nickthelegend/ripar-wallet/docs/FIRMWARE.md

# Ripar Wallet: firmware guide

The firmware turns a Waveshare ESP32-S3-LCD-2 into an air-gapped signer. Its radio is off. Requests arrive as QR codes through the camera, and every answer leaves as one QR code on the screen. Nothing is signed until the user has seen every line of the review, held a thumb on the pulse sensor until a live pulse is measured, and then pressed SIGN.

- **Protocol:** byte-exact contract in [`PROTOCOL.md`](PROTOCOL.md).
- **Bluetooth fallback:** the builds `env:ripar` and `env:ripar-ble` can also carry the same QR text over Bluetooth LE when the camera cannot read the codes. The radio stays dead until the user turns it on in the device menu (review + pulse + SIGN), and every screen shows **RADIO ON** while it is alive. `env:ripar-airgap` is the same firmware without any radio code. Contract: [`BLE_LINK.md`](BLE_LINK.md); on the device: [BLE LINK](#ble-link-bluetooth-fallback).
- **Wi-Fi test link (TEMPORARY TEST FEATURE):** the default build `env:ripar` also contains a Wi-Fi courier for testing (`RIPAR_WIFI=1`): the network is sent by the paired phone over Bluetooth and confirmed on the device, Wi-Fi runs only after **WI-FI ON** in the menu, and every screen shows **WIFI ON** while it is alive. **For the air-gapped pitch firmware flash `env:ripar-airgap`** (or `env:ripar-ble` for Bluetooth without Wi-Fi). Contract: [`WIFI_LINK.md`](WIFI_LINK.md); on the device: [Wi-Fi test link](#wi-fi-test-link-temporary).
- **Wiring:** full pin list in [`WIRING.md`](WIRING.md).
- **Source:** `firmware/` (PlatformIO, Arduino-ESP32 2.0.17 / ESP-IDF 4.4).

> **Status (2026-09-27, firmware v1.2).** The full firmware builds and links. The host tests cover the portable code, including the screen state machine, the signing gate, the SIGN step (byte-equal to the Python reference) and the vault derivation, and they pass. Firmware v1.2 compiles in the Ripar contract addresses, derives the vault from K1, stores context layout v3 and enforces PANIC FIRST ([PROTOCOL.md §7](PROTOCOL.md#7-changes-in-firmware-v12)). The findings of the second security and conformance review (panic epoch, re-pairing, key presses across screens, device-time ratchet, sentinel, revoke display) are fixed in code and tests; what stays open is listed under [Known limitations](#known-limitations). The QR frames drawn by `companion_lite.html` decode with the firmware's own quirc + UR decoder + parser on the PC. **Nothing in this guide has been checked on a real board yet**: the display rotation, the camera orientation, the pulse-sensor tuning and the key timings are all untested. See [Known limitations](#known-limitations).

## Contents

1. [Hardware and wiring](#1-hardware-and-wiring)
2. [Build and test](#2-build-and-test)
3. [Flash over USB-C](#3-flash-over-usb-c)
4. [First boot](#4-first-boot)
5. [Screens and keys](#5-screens-and-keys)
6. [Walkthrough](#6-walkthrough)
7. [Security model](#7-security-model)
8. [Known limitations](#known-limitations)
9. [Source map](#9-source-map)

## 1. Hardware and wiring

| Part | Connection | Notes |
|---|---|---|
| Waveshare ESP32-S3-LCD-2 | - | ESP32-S3R8 (8 MB octal PSRAM), 16 MB flash, 2" ST7789 LCD used landscape at 320×240 |
| OV5640 camera | 24-pin FPC on the back | grayscale QVGA, powered down between scans |
| MAX30102 pulse sensor | VIN → 3V3 (P2-1), GND → P2-2, SDA → **GPIO48** (P2-6), SCL → **GPIO47** (P2-5), INT open | shares the I2C bus with the on-board IMU (0x6B). **Move its pull-up jumper to 3.3 V.** |
| Buzzer (active, 3.3 V) | + → **GPIO18** (P1-6), − → GND | use an S8050 + 1 k base resistor for a 5 V buzzer or one drawing more than 20 mA |
| SIGN key | the board's **BOOT key (GPIO0)**, pressed by the printed Sign_Pin | a strapping pin: **never hold it while powering on** |
| Battery | 18650 → TP4056 → latching switch → board BAT connector | the gauge reads GPIO5 through the board's 200 k / 100 k divider |

With the camera attached, the only free signals are GPIO18, GPIO43 and GPIO44, plus the shared I2C bus. `firmware/include/board.h` holds every pin.

## 2. Build and test

Requirements: PlatformIO Core and Python 3 (standard library only). `lib_deps` fetches LovyanGFX once. The quirc QR decoder is vendored in `firmware/lib/quirc`.

```bash
cd firmware
pio run -e ripar            # TEST build (default): QR + Bluetooth LE fallback + Wi-Fi test link -> .pio/build/ripar/firmware.bin
pio run -e ripar-ble        # QR + Bluetooth LE fallback, no Wi-Fi code -> .pio/build/ripar-ble/firmware.bin
pio run -e ripar-airgap     # the air-gapped firmware, no radio code at all -> .pio/build/ripar-airgap/firmware.bin
pio run -e chk_device       # device bring-up check (no signing code), see test/device/check_main.cpp
python test/host/run_host_tests.py          # portable modules, MinGW / any g++ as C++14
python tools/make_request.py selftest       # companion tool: build -> simulate -> verify, tamper tests
python tools/make_request.py check-vectors  # test/host/vectors_protocol.h matches the Python reference
python tools/ref_eip712.py check            # test/host/vectors_eip712_abi.h matches the Python reference
```

- The host suites are `test_ble_link`, `test_cbor_ur`, `test_crypto`, `test_eip712_abi`, `test_fsm`, `test_hashes`, `test_policy`, `test_protocol`, `test_pulse`, `test_respond`, `test_vault` and `test_wifi_link`.
- Three firmware builds (the only differences are `RIPAR_BLE` and `RIPAR_WIFI`):

| Env | `RIPAR_BLE` | `RIPAR_WIFI` | What it is | Last build (2026-09-28), of 327 680 B RAM / 6 553 600 B flash |
|---|---|---|---|---|
| `ripar` (default) | 1 | 1 | **test build**: QR + the Bluetooth LE fallback courier + the Wi-Fi test link (`src/wifi_link.cpp`, `src/wifi_proto.cpp`) | RAM 27.5 % (90 024 B), flash 26.8 % (1 759 157 B) |
| `ripar-ble` | 1 | 0 | QR + the Bluetooth LE fallback courier (`src/ble_link.cpp`, `src/ble_proto.cpp`); no Wi-Fi code linked | RAM 20.3 % (66 568 B), flash 20.5 % (1 345 909 B) |
| `ripar-airgap` | 0 | 0 | **the air-gapped firmware**: no BLE / Wi-Fi source built, no Bluetooth / Wi-Fi code linked ([radio check](#7-security-model)) | RAM 12.1 % (39 572 B), flash 11.3 % (738 921 B) |

- The sizes are static RAM and flash in the default 16 MB partition table. While a radio is on, Bluedroid / the Wi-Fi driver and lwIP also allocate heap (not measured on hardware). The ERC1967Proxy creation code of the vault derivation (1008 bytes) lives in flash.
- `pio run -t compiledb` without the same `PLATFORMIO_BUILD_FLAGS` as the last build changes the configuration hash, and PlatformIO then empties `.pio/build/<env>`: build again afterwards.
- A low-disk PC can add `PLATFORMIO_BUILD_FLAGS=-pipe` so that GCC keeps its temporary files in memory. Run one `pio` build at a time.
- Optional build flags (add them to `build_flags`):

| Flag | Default | Meaning |
|---|---|---|
| `RIPAR_BLE` | 1 in `ripar` and `ripar-ble`, 0 in `ripar-airgap` | The Bluetooth LE fallback courier ([BLE_LINK.md](BLE_LINK.md)). Use the envs rather than setting it by hand: `ripar-airgap` also leaves the BLE sources out. |
| `RIPAR_WIFI` | 1 in `ripar`, 0 in `ripar-ble` and `ripar-airgap` | The Wi-Fi test link ([WIFI_LINK.md](WIFI_LINK.md)), a TEMPORARY TEST FEATURE. Needs `RIPAR_BLE=1`. Use the envs: `ripar-ble` / `ripar-airgap` also leave the Wi-Fi sources and libraries out. |
| `RIPAR_LCD_ROTATION` | 1 | Use 3 if the screen is upside down. |
| `RIPAR_CAM_VFLIP` / `RIPAR_CAM_HMIRROR` | 1 / 0 | Viewfinder orientation. QR decoding works either way. |
| `RIPAR_CAM_AE_LEVEL` | -2 | Camera exposure. Go darker (down to -4) if phone screens wash out. |
| `RIPAR_PULSE_STRICT` | 0 on the device, 1 in the emulator | 1 adds the strict anti-spoof liveness tests (beat-timing variability, pulse shape, IR/red cross-timing) to the standard pulse gate. **Off on the device**: on the first hardware test they rejected a real resting thumb (82 bpm, very low beat-to-beat variability). See [Pulse gate: standard and strict](#pulse-gate-standard-and-strict). |
| `RIPAR_CHECK_START_PULSE` / `RIPAR_CHECK_RAW` | unset | `chk_device` only: start on the pulse screen / stream raw MAX30102 samples (`raw,<n>,<ir>,<red>` at 100 Hz) for `tools/pulse_replay`. |
| `RIPAR_LED_CHALLENGE` | 0 | 1 also requires the MAX30102 LED-drive liveness challenge before SIGN is armed. Not tested on hardware. |
| `RIPAR_TIME_FLOOR` | 2026-09-26 00:00 UTC | The earliest "now" the device assumes (see [co-sign expiry](#co-sign)). |

## 3. Flash over USB-C

Use the board's own USB-C port, not the charge-only TP4056 port. Never plug both at once.

```bash
cd firmware
pio run -e ripar -t upload          # builds if needed, then flashes over the native USB (USB-Serial/JTAG)
pio device monitor -b 115200        # optional: status lines (self-test, K1 address, "output <type>")
```

**If the upload cannot connect** (a crashed app, or a USB port that no longer enumerates), use ROM download mode:

1. Hold **BOOT**.
2. Press and release **RST**.
3. Release **BOOT**. The chip now waits in ROM download mode, and the screen stays dark.
4. Run `pio run -e ripar -t upload` again.
5. Press **RST** to start the new firmware.

`ripar` is the **test build** (with the temporary Wi-Fi test link). For a demo, a pitch or funds flash `pio run -e ripar-airgap -t upload` (no radio code) or `-e ripar-ble` (Bluetooth fallback, no Wi-Fi code).

A normal upload does not touch the NVS partition, so the seed and the pairing survive re-flashing (and so does a stored Wi-Fi network: FORGET WI-FI before flashing another build if its password matters).

> **`pio run -t erase` erases the whole flash, including the seed.** The device then creates new keys, which means a new K1 address and a new vault owner. There is no seed backup yet (see [Known limitations](#known-limitations)). Only erase a unit that holds no funds.

## 4. First boot

| Step | What you see | What happens |
|---|---|---|
| 1 | RIPAR logo, "starting..." | The display, key, buzzer, pulse sensor (I2C 0x57) and camera are probed. |
| 2 | "self-test: crypto vectors..." | `keys_selftest()` checks the on-device crypto against published vectors (RFC 6979 P-256, the secp256k1 "Satoshi" vector, BIP-32 and SLIP-10 test vector 1) and cross-checks it with mbedTLS. |
| 3 | First run only: "NEW DEVICE: creating keys..." | 64 TRNG bytes, 1.5 s of raw MAX30102 samples, camera frames and timing jitter are hashed into the seed input. `keys_create()` adds 64 more TRNG bytes. The seed goes to NVS, and the self-test runs again, now signing and verifying with the new device keys. |
| 4 | Home screen | Shows the short K1 address, battery level and **NOT PAIRED**. The serial log prints the K1 address and the vault derived from it (`ripar: K1 0x…, vault 0x…, not paired`). |

**Your vault.** The device's vault is fixed by its keys: the MetaMask HybridDeleGator owned by K1, at the address the canonical SimpleFactory deploys it to (CREATE2, salt 0, [PROTOCOL.md §2.1](PROTOCOL.md#21-the-vault-derived-from-k1)). The device derives it itself and pins no other vault, so read it from the device before funding anything: the pairing review shows it as `Vault 0x… (derived from this device)`, and `make_request.py parse @pair.txt` prints it as `vault` (or `make_request.py vault <K1 address>` from the keys-only pairing QR). A new seed (erased flash) means a new K1 and therefore a new vault.

**After a firmware update from v1.1** the stored context (layout v2) is not loaded: the boot screen says **PAIRING LOST**. Pair again with the counter floors ([Known limitations](#known-limitations), "Lost context").

If the self-test fails, the screen shows **SELFTEST FAIL**, the failed checks and "SIGNING IS DISABLED". This state is final until the next reset: no key does anything and nothing is ever signed. The serial log lists the same lines.

The pulse sensor and the camera are optional at boot:
- Without the camera the device cannot scan anything.
- Without the pulse sensor it can still answer deny requests and PANIC, but it can sign nothing that needs the pulse.

## 5. Screens and keys

There is one key, SIGN (BOOT). It produces three events:
- **press**: released within 1 s.
- **hold 2 s**: fires while the key is held, at 2 s.
- **hold 5 s**: fires at 5 s. A 5 s hold also fires "hold 2 s" first.

A release between 1 s and 2 s does nothing.

**A press or hold belongs to the screen on which it began.** After any screen change the key does nothing until it has been released: queued events are dropped, a press that is still held is swallowed until release (`io_flush`), and the state machine also ignores key events until it has seen the key up on the new screen. The only exception is the Hold screen on Home, which exists for the hold that opened it. So a hold that cancels a screen never turns into a PANIC on Home, a hold carried into a co-sign review never files a deny, and a SIGN press that began while the pulse was being measured does not sign when ARMED appears: press again.

Every screen except Home returns to Home after 120 s without a key press. The buzzer gives:
- a short tick for each new QR part and each heartbeat;
- a rising two-tone for OK;
- a falling two-tone for refused or error.

| Screen | Shows | press | hold 2 s | hold 5 s |
|---|---|---|---|---|
| **Home** | K1 (short), battery, PAIRED / NOT PAIRED | scan a request | opens the Hold screen | (only through the Hold screen) |
| Hold (on Home) | "RELEASE = PAIRING QR", keep holding = PANIC | - | (release before 5 s = **pairing QR**, keys only) | **PANIC**, signed at once |
| **Scan** | camera viewfinder, multipart progress bar, hint | - | cancel → Home | - |
| **Review** | every line of the request, paged by display row; arrows and a scrollbar whenever rows are hidden | next page; on the last page: continue (→ Pulse), or sign a deny; refused → Home | co-sign review: **DENY**; other reviews: cancel → Home | - |
| **Pulse** | heart, bpm, beats n/5, progress ring | ignored (error beep) | cancel → Home | - |
| **Armed** | "PULSE OK - press SIGN" | **SIGN**, only while the pulse still counts as live | cancel → Home | - |
| **QR** | the signed response | done → Home | done → Home | - |
| Message | refusal or error, with the exact reason | → Home | → Home | - |
| Pairing QR | `ripar-pair` with K1 + P1 + firmware id (nothing signed, nothing pinned) | → Home | device menu | - |
| Device menu | REVOKE the last mandate / REOPEN the agent lane / (`ripar`, `ripar-ble`) BLE LINK or BLE OFF / FORGET PHONE / (`ripar` only) WI-FI ON or WI-FI OFF / FORGET WI-FI / BACK | next item | select | - |
| BLE pairing (`ripar`, `ripar-ble`) | advertised name `RIPAR-XXXX`, link state; during a pairing the 6-digit code, large | no code: → Home (radio stays on); code: **confirm** it | no code: **radio off**; code: **reject** it | - |

**RADIO ON / WIFI ON badge** (`ripar`, `ripar-ble`). While the Bluetooth controller is alive, every screen carries a red **RADIO ON** badge in the top-right corner; while the Wi-Fi driver is alive (`ripar` only) it says **WIFI ON**, and **BLE+WIFI** when both are. Home then says **NOT AIR-GAPPED** instead of AIR-GAPPED. The badge is drawn by the display flush itself (`ui.cpp`), so no screen appears without it, and it follows the driver state (`esp_bt_controller_get_status()`, `esp_wifi_get_mode()`, compared every 100 ms), not a flag. On SCAN with a link on, the hint says the request can also come from the phone (`BLE`, `Wi-Fi` or `BLE / Wi-Fi`). While Wi-Fi is on, Home also shows one amber line with the device's address (or the connection state) and the 8-digit **link code** every HTTP request needs.

**JOIN WI-FI and WI-FI ON reviews** (`ripar` only) are device settings, not signatures: once every row has been shown, a press confirms them **without the pulse**; hold 2 s rejects (state machine: `Job::WifiJoin` / `Job::WifiOn` → `Act::Confirm`).

The review shows at most 9 rows at a time. Each press moves the page by 8 rows, overlapping one row, so every row appears on screen. The last-page footer (for example "press = PULSE + SIGN") appears only once the last row has been drawn. Until then the footer reads "press = more", and SIGN cannot be armed.

A refused request still opens its review. Its first line is **REFUSED** in red, with the policy's exact reason: wrong chain, a contract that is not pinned, a vault that is not the device's, an expiry too far ahead, UNKNOWN CALLDATA, MANDATE WITHOUT PULSE CO-SIGN, PANIC FIRST, and so on. A request that cannot even be parsed goes straight to a message screen with the parser's reason.

Review lines added in firmware v1.2:

| Review | Line | Meaning |
|---|---|---|
| Pairing | `Registry` / `Co-sign` / `Relay` `0x… (firmware table)` (green) | the address compiled into the firmware; any other is refused |
| Pairing | `Vault 0x… (derived from this device)` (green) | the vault derived from K1, the only one the device pins |
| Pairing | `Key 8 vault 0x… (NOT THIS DEVICE'S VAULT)` (red) | the request named another vault: refused |
| Pairing | `CHANGES FORGETS mandate 0x… (killed once this device's last PANIC is relayed)` | a re-pairing to another chain after a panic |
| Pairing | `PANIC mandates signed on <chain> die only once this device's PANIC (min epoch N) is relayed there - this device cannot check that. Confirm only if the on-chain min epoch of this device key is >= N` (red) | a pairing that moves the chain (manager, enforcer, vault) after a panic: the device cannot see whether the panic was relayed |
| Mandate | `Agent id 42 (companion)` | the agent a deny is filed against, as sent by the companion |
| Mandate | `Period never resets (lifetime cap)`, or `Period 86400 s = 1 d (fixed windows from the first AUTO spend)` | the AUTO period of the pulse caveat |
| Mandate, co-sign | `Vault 0x… (derived from this device)` (green; another vault is red and refused) | |
| Co-sign | `0x<payee> becomes an AUTO payee of this mandate: the agent can then pay it without a pulse, up to 25 AUSD per payment and 50 AUSD per 86400 s = 1 d window (fixed windows from the first AUTO spend)` (amber) | signing whitelists the payee for the AUTO path of the remembered mandate; shown exactly when the enforcer will record it (a `transfer` of the mandate's token with amount > 0, or a native send with value > 0 under native terms, to a non-zero payee, while the mandate sets `newPayeeNeedsHuman`); never on a refused co-sign |
| Co-sign | `0x<payee> may become an AUTO payee of mandate 0x…: the agent could then pay it without a pulse, up to caps this device does not know` (amber) | a co-sign for a mandate the device does not remember (UNKNOWN MANDATE: older, revoked, from before a re-pairing) whose call could be meterable under some terms (native send with value > 0, or a `transfer` with amount > 0) |
| Co-sign | `this device signed a PANIC after this mandate: once that PANIC is relayed, the chain refuses it` (amber) | |

## 6. Walkthrough

Two tools run on the online computer, which is untrusted:
- `firmware/tools/make_request.py` builds requests and verifies responses.
- `firmware/tools/companion_lite.html` shows the request QR codes and prepares the verify command.

The commands below use bash syntax (Git Bash on Windows works) and are run from `firmware/`. Addresses in `<...>` are your deployed contracts.

**companion_lite.html:**
1. Open the file in a browser. It needs cdnjs for its QR encoder.
2. Paste the output of `make_request.py build` (or load the saved file) and press **Show QR**. Multipart requests loop at about 300 ms per frame; the slider changes the speed.
3. Point the device at it after pressing SIGN on the Home screen.
4. Read the device's answer with any QR reader (a phone camera works), paste it in section 3, and run the command the page prints.

Before using real hardware, `python tools/make_request.py simulate @req.txt` plays a demo device (fixed demo seed, **no pulse check and no pinned-context policy**). It does refuse what the firmware refuses whatever it has pinned: contracts other than the compiled-in ones, a vault other than its own (the demo vault `0xc36F625D426eBa8f1e0129276B284a939CD3A57D`, see `demo-keys`), token-table and Privy allow-list violations. Use it to check a request file and your verify command.

### Pairing

Pairing pins the chain and contracts that every later request is checked against.

```bash
python tools/make_request.py build pair chainId=10143 sentinel=<SENTINEL> > req_pair.txt
```

- The DelegationManager, PulseCosignEnforcer, RiparDeviceRegistry and RiparReputationRelay are compiled into the firmware for 10143 and 143 (PROTOCOL.md §4): `build pair` fills in the registry, the device pins the others. Naming any other address (`registry=`, `manager=`, `enforcer=`, `relay=`) makes the device refuse the pairing.
- Leave `vault` out: the device pins the vault it derives from its K1. `vault=<address>` is only accepted when it is exactly that vault (a check that the companion computed the same account).
- `now` (the companion clock) is added automatically.

On the device:
1. Scan the request.
2. Review every contract to pin. The compiled-in ones are marked "(firmware table)" in green, the vault "(derived from this device)". Anything missing is shown as a warning, for example "not set - no reopen, mandates without a sentinel lane".
3. Press on the last page, hold your thumb on the sensor, and press SIGN when the screen says so.

P1 and K1 both sign `BindDevice(K1, P1)`. The device stores the new context and only then shows the QR. If NVS fails, the signature is withheld.

**Pairing again** shows "REPLACES the current pairing" and one red **CHANGES** line per pinned value that changes (old → new). **PANIC FIRST:** while a mandate the device signed since its last panic may be live, a pairing that changes the chain, DelegationManager, PulseCosignEnforcer or vault is refused ("PANIC FIRST: mandates signed on … would not be covered by PANIC after re-pairing"). Sign a PANIC (Home: hold 5 s), relay it, then pair again. A revoke is not enough, because earlier mandates may still be live. With the compiled-in contracts and the derived vault this only concerns a change of chain; the sentinel may change at any time. PANIC FIRST clears when the panic is **signed**: a chain move after a panic shows a red **PANIC** line, because the old mandates die only once the panic is **relayed** - check the on-chain min epoch before confirming.

**Counter floors** (`minEpoch=<n> reopenNonce=<n>`, pair-req keys 10 and 11) can only raise the device's panic epoch and reopen nonce. The review shows both counters and marks a raise in amber. Use them when the device lost its context (the boot screen then says **PAIRING LOST**), see [Known limitations](#known-limitations).

Save the answer (`UR:RIPAR-PAIR/...`) as `pair.txt`, then verify it:

```bash
python tools/make_request.py parse @pair.txt --req @req_pair.txt      # exit 0 = VERIFIED; prints k1Address, vault, p1Key
VAULT=$(python tools/make_request.py parse @pair.txt | python -c "import json,sys; print(json.load(sys.stdin)['vault'])")
```

`pair.txt` now holds the device's K1 address and P1 key, and with them its vault. Every later `parse` uses it through `--pair @pair.txt`, and also checks that a mandate, co-sign or reopen names this vault. Deploy and fund exactly `$VAULT` (the MetaMask smart-accounts kit computes the same address for owner K1 and salt `0x`).

The **pairing QR** from the Home screen (hold 2 s, release) contains the same keys **without** signatures, and it pins nothing.

### Mandate (K1 signs a delegation)

```bash
P1=$(python tools/make_request.py parse @pair.txt | python -c "import json,sys; print(json.load(sys.stdin)['p1Key'])")
python tools/make_request.py build mandate chainId=10143 manager=0xdb9B1e94B5b69Df7e401DDbedE43491141047dB3 \
    delegate=<AGENT_REDEEMER> delegator=$VAULT salt=1 agentId=42 label="demo agent" \
    "caveats=[{\"kind\":\"pulse\",\"p1Key\":\"$P1\",
      \"token\":\"0xa9012a055bd4e0eDfF8Ce09f960291C09D5322dC\",\"perTxAutoCap\":5000000,
      \"periodAutoCap\":20000000,\"period\":86400,\"epoch\":0,\"newPayeeNeedsHuman\":true,\"sentinel\":\"<SENTINEL>\"}]" \
    > req_mandate.txt
```

The device signs a mandate only if:
- it has **exactly one** caveat on the pinned PulseCosignEnforcer, naming **this** device's P1 key, an epoch **exactly equal** to the device's panic floor, and exactly the pinned sentinel (the zero address when none is pinned);
  - the panic floor is 0 on a new device and N after the device signed `Panic(N)` (or after a pairing floor of N). The review shows it as "(= panic floor)"; any other epoch is refused, because the device's next PANIC (floor + 1) could not kill a higher one;
- every other caveat is one it can decode and show;
- the delegator is the device's own vault (the vault derived from K1);
- the delegate is not ANY_DELEGATE.

The pulse caveat's enforcer defaults to the compiled-in PulseCosignEnforcer (`0x64d61fe5438981DC803ED61250FEf024617ae7eE`), the only one the device accepts on 10143 and 143.

The review shows every decoded caveat field. The agent id is marked "(companion)". The AUTO period reads "never resets (lifetime cap)" for 0, otherwise the duration and "(fixed windows from the first AUTO spend)": a window starts at the first AUTO spend and is fixed, so up to twice `periodAutoCap` can leave within seconds across a window boundary (contracts/SPEC.md v1.2).

After pulse + SIGN, the device stores `lastDelegationHash` (what REVOKE revokes), the agent id (what a deny is filed against) and the mandate's pulse terms (for the co-sign review), marks that a mandate was signed since the last panic (PANIC FIRST), then shows an `eth-signature`.

```bash
python tools/make_request.py parse @mandate.txt --req @req_mandate.txt --pair @pair.txt   # prints delegationHash
```

### Co-sign

A co-sign is a payment the agent cannot make alone.

```bash
EXP=$(( $(date +%s) + 3600 ))      # must be at most 7 days after the device's "not before" time
python tools/make_request.py build cosign chainId=10143 \
    delegationHash=0x<delegationHash from the mandate> delegator=$VAULT redeemer=<AGENT_REDEEMER> \
    target=0xa9012a055bd4e0eDfF8Ce09f960291C09D5322dC value=0 nonce=1 expiry=$EXP \
    'transfer={"to":"<PAYEE>","amount":25000000}' \
    'ai={"text":"pay invoice 17","claims":{"to":"<PAYEE>","token":"0xa9012a055bd4e0eDfF8Ce09f960291C09D5322dC","amount":25000000}}' \
    > req_cosign.txt
```

The review shows:
- the action;
- the amount, using the firmware token table (AUSD has 6 decimals, so 25000000 is shown as "25 AUSD");
- the full payee address, chain, vault ("derived from this device"), redeemer and mandate hash;
- for the mandate this device signed last, whether signing whitelists the payee: "0x… becomes an AUTO payee of this mandate: the agent can then pay it without a pulse, up to … per payment and … per … window" (PulseCosignEnforcer v1.2: a co-signed `transfer` of the mandate's token, or native send under native terms, with a non-zero amount, while the mandate sets `newPayeeNeedsHuman`). Read it before signing: after this co-sign the agent can pay that payee on its own, within the caps;
- expiry in UTC, and the nonce (use a fresh nonce for every co-sign: the enforcer consumes it per mandate);
- the AI claim check (MATCH or MISMATCH);
- anything the companion added, marked "(companion)".

The enforcer defaults to the compiled-in PulseCosignEnforcer.

After pulse + SIGN, P1 signs `HumanApproval`, with `presenceHash = sha256(evidence12 ‖ salt16)` and a fresh salt.

```bash
python tools/make_request.py parse @cosign.txt --req @req_cosign.txt --pair @pair.txt   # prints caveatArgs
```

**Expiry and device time.** The device has no clock. Its "not before" time is the later of:
- the build floor;
- the pairing time (key 9);
- the expiry of each co-sign it signed, but each co-sign moves the time forward by **at most 1 day**, so approved co-signs cannot push the device time (and with it the 7-day expiry window) far ahead of real time.

A device whose time has fallen more than a week behind (no co-signs for a while, or fewer than about one a day) refuses every co-sign until it is paired again, because pairing updates the time. A pairing time more than 30 days after the device time is shown in red.

### Deny (report the agent)

On a co-sign review, **hold 2 s**. The device builds the deny itself:
- the pinned chain and relay;
- the agent of the pinned mandate;
- `requestHash = hashStruct(HumanApproval)` of the request it just reviewed.

It shows that deny. A press signs it, **without the pulse**, because a deny can only restrict.

```bash
python tools/make_request.py parse @deny.txt --req @req_cosign.txt --pair @pair.txt     # relay: the firmware's for the chain
```

A deny request from the companion (`build deny chainId=... relay=... agentId=... requestHash=...`) is refused unless its agent is the pinned one. It is reviewed and signed the same way.

### Privy authorization

```bash
python tools/make_request.py build privy 'json={"body":{"policy_ids":["pol9x2k4m8"]},"headers":{"privy-app-id":"cm0appid1234"},"method":"PATCH","url":"https://api.privy.io/v1/wallets/wl8yz4c2rq0q1cdz2q8a4","version":1}' > req_privy.txt
python tools/make_request.py parse @privy.txt --req @req_privy.txt --pair @pair.txt
```

- Only the two allow-listed request shapes are accepted: a wallet's signers or policies, and a key quorum. Everything else is refused.
- Every value is shown in full. Key-quorum keys are marked THIS DEVICE or OTHER P-256 KEY.
- After pulse + SIGN, P1 signs `sha256` of the exact JSON bytes and returns a DER signature.

### PANIC, revoke, reopen

These are started on the device and use the **pinned** contracts only.

| Action | How | Pulse? | Verify |
|---|---|---|---|
| PANIC | Home: hold SIGN. At 2 s the Hold screen appears; keep holding to 5 s. Signs `Panic(minEpoch + 1)` at once; refused if not paired. A hold that began on another screen never panics. Clears PANIC FIRST | no | `parse @panic.txt --pair @pair.txt --chain 10143` (the compiled-in enforcer) |
| Revoke | Home: hold 2 s and release, then hold 2 s on the pairing QR → **REVOKE**. Revokes the last mandate this device signed, then forgets it: scan the QR before leaving the screen. Does not clear PANIC FIRST | yes | `parse @revoke.txt --pair @pair.txt --chain 10143` |
| Reopen | same menu → **REOPEN**. Nonce = last + 1, never reused; needs a pinned sentinel; names the device's vault | yes | `parse @reopen.txt --pair @pair.txt --chain 10143 --contract <SENTINEL>` |

PANIC also turns the Bluetooth radio and Wi-Fi off first (`ripar` / `ripar-ble` builds) and clears the persisted WI-FI ON choice.

Relay a PANIC QR at once. The device never lowers its epoch: every later mandate needs `epoch =` the new minimum. If the new epoch cannot be stored in NVS, the QR is still shown with a warning, and the device keeps using the new epoch until it restarts.

### BLE LINK (Bluetooth fallback)

`ripar` build only; the protocol, security model and phone flow are in [BLE_LINK.md](BLE_LINK.md). QR stays the primary path: use this only when the camera cannot read the companion's codes.

| Action | How | Pulse? |
|---|---|---|
| Radio on | device menu (Home: hold 2 s and release, then hold 2 s on the pairing QR) → **BLE LINK** → review "Turns the radio ON. Ripar is not air-gapped while it is on." → pulse + SIGN (a confirmation, nothing is signed) → the **BLE pairing** screen | yes |
| Pair a phone | on the BLE pairing screen only: connect from the Ripar app, compare the 6-digit code with the phone, press SIGN to confirm (hold 2 s = reject). A new pairing replaces the paired phone | - |
| Send a request | Home: press (SCAN). The app writes the UR parts; the device takes them exactly like camera QR parts: same review, pulse and SIGN. The response QR is also sent to the phone | as the request |
| Radio off | menu **BLE OFF**, hold 2 s on the pairing screen (no code shown), PANIC, 5 min without link traffic, power off | no |
| Forget the phone | menu **FORGET PHONE**: deletes the bond now (radio on) or before the radio is next turned on | no |

The Bluetooth controller is never initialised at boot. Turning the radio off disables and de-initialises Bluedroid and the controller; the controller memory stays reserved so it can be turned on again without a reboot.

### Wi-Fi test link (temporary)

`ripar` build only, a **TEMPORARY TEST FEATURE**; protocol, security model and phone flow in [WIFI_LINK.md](WIFI_LINK.md). For the air-gapped pitch firmware flash `ripar-airgap` (or `ripar-ble`).

| Action | How | Pulse? |
|---|---|---|
| Store a network | BLE LINK and pair the phone first. With the device on Home (or the BLE pairing screen), the app writes `{"v":1,"ssid":...,"pass":...}` to the PROV characteristic → review **JOIN WI-FI &lt;ssid&gt;?** (the password is never shown) → press SIGN to store it (NVS `ripar-wifi`); hold 2 s rejects | no |
| Wi-Fi on | device menu → **WI-FI ON** → review "turns Wi-Fi ON. Ripar is not air-gapped while it is on" → press SIGN. The choice is persisted: Wi-Fi also starts after a restart | no |
| Use it | Home shows `192.168.1.23  CODE 1234 5678`: every HTTP request needs `X-Ripar-Code: 12345678` (a new code at every boot). `GET /status`, `POST /rx` (UR lines, only on SCAN), `GET /tx` (the QR on screen) | as the request |
| Wi-Fi off | menu **WI-FI OFF**, **FORGET WI-FI** (also erases the network), PANIC. All three clear the persisted choice | no |

Wi-Fi never starts without a stored network **and** the WI-FI ON choice. It has no idle timeout (a developer may keep it on), and it may run together with Bluetooth (the framework is built with Wi-Fi / BLE coexistence).

## Pulse gate: standard and strict

**First hardware test, 2026-09-28** (Waveshare ESP32-S3-Touch-LCD-2 + MAX30102, `chk_device`):
- The crypto self-test passed on the chip, including every mbedTLS cross-check.
- The MAX30102 answered on the I2C bus (PART_ID 0x15) once SDA went to GPIO48 and SCL to GPIO47.
- It measured a resting thumb at **82–85 bpm with 11–12 beats per 8 s window**. The IR DC was 118k, well above the 50k finger threshold.

The v1.2 strict liveness tests never let that real pulse pass. They were tuned on synthetic signals, and a resting heart can be as regular as they assume a spoof is (beat-to-beat jitter about 0.03). The device therefore runs two gates:

| Gate | Requires | Used by |
|---|---|---|
| **Standard** | All of these: <br>• a finger (IR DC above 50k); <br>• at least 5 beats in the 8 s window, at 40–180 bpm; <br>• a rhythm (interval jitter ≤ 0.35); <br>• a beat within the last 2.5 intervals; <br>• no ADC clipping, and both channels moving; <br>• IR and red pulses correlated (r > 0.5). | the device (`RIPAR_PULSE_STRICT=0`, default) |
| **Strict** | The standard gate plus the "too regular" timing statistics, the beat-shape screen and the IR/red cross-timing test (host-tested against square, sine, triangle, rate-step and replayed-shape spoofs) | the emulator and the host tests; the device with `RIPAR_PULSE_STRICT=1` |

**Tuning strict mode on real data:**

```bash
# record 60 s of your thumb as raw samples (the screen shows RAW RECORDING)
PLATFORMIO_BUILD_FLAGS="-DRIPAR_CHECK_START_PULSE=1 -DRIPAR_CHECK_RAW=1" pio run -e chk_device -t upload
pio device monitor -b 115200 > capture.txt
# replay it through both gates
g++ -std=c++14 -O2 -Iinclude tools/pulse_replay.cpp src/pulse_algo.cpp -o pulse_replay && ./pulse_replay capture.txt
```

**What the standard gate still stops:** no finger, a finger without a pulse, a constant signal, rates below 40 or above 180 bpm, and an irregular rhythm. All of these are host-tested.

**What it no longer stops:** a synthetic optical source driving both LEDs' reflections in step, such as a perfectly periodic "fake finger". Resisting that needs the strict tests tuned on recorded data, or a hardware liveness signal (`RIPAR_LED_CHALLENGE`).

## 7. Security model

**What is trusted.** Only the device: its firmware, its keys, and the contracts pinned at a pairing the user confirmed. Everything else is an untrusted courier: the companion, the agent, Privy, and this guide's tools. A courier can refuse to relay, but it cannot get the device to sign anything the user did not see.

**What the device enforces** (portable code, host-tested):

- **Strict parsing:**
  - CBOR is bounded and canonical;
  - strict JSON is used for Privy;
  - unknown keys are refused;
  - request ids are 16 bytes, and the authority must be ROOT.
- **Digests are rebuilt on the device.** Every digest comes from the same parsed struct that produced the review lines (`review.h`). The device never signs a hash it was handed.
  - The SIGN step (`respond.h`) repeats the policy check, rebuilds the digest and builds the response. Its output is tested byte for byte against the independent Python reference for every request type.
- **Pinned context** (`context.h`, `policy.h`):
  - Chain, DelegationManager, PulseCosignEnforcer, sentinel, relay, registry and vault are pinned only at pairing. The DelegationManager, PulseCosignEnforcer, registry and relay can only be the addresses compiled into the firmware, and the vault only the one derived from K1 (`vault.h`, host-tested against an on-chain known answer). A re-pairing lists every changed value in red and is refused while it would move mandates signed since the last panic out of that panic's reach (PANIC FIRST).
  - A request naming anything else is refused; so is a mandate or co-sign for any other vault.
  - Co-sign, deny and Privy requests never change the pinned contracts or the mandate. A co-sign only advances the device time, by at most 1 day.
  - The panic epoch and the reopen nonce only ever increase. Every mandate carries exactly the current panic floor, so the next PANIC kills every mandate the device signed.
- **What gets refused:**
  - calldata the device cannot decode;
  - an ERC-20 call that also carries native value;
  - a token whose decimals or symbol claim disagrees with the firmware table;
  - a mandate without exactly one pulse co-sign caveat for this device;
  - any caveat without a strict terms decoder;
  - an expiry beyond the 7-day window;
  - any Privy request outside the allow-list.
- **The signing gate** (`fsm.h`, `test_fsm.cpp`, security review B1):
  - SIGN is armed only after every review row has been drawn, the policy check has passed, and a live pulse has been measured.
  - The signature is made only for a press read in the **same** loop pass in which the pulse sensor still reports a live pulse.
  - Nothing is remembered between passes. A press or hold only acts on the screen on which it began (see [Screens and keys](#5-screens-and-keys)).
  - Deny and PANIC skip the pulse, because they can only restrict.
- **Pulse evidence:**
  - a live pulse means at least 5 beats in 8 s at 40–180 bpm, with a finger present and samples still arriving;
  - it must not look like a signal generator: no flat / saturated / uncorrelated channels, no square-wave (also judged against the sensor noise) or sine / triangle upstrokes, no perfectly regular rhythm, and (since the v1.2 review) beat-to-beat variability that the IR and red channels **share** - sensor noise moves each channel's beats independently, a heart moves both (PROTOCOL.md §5);
  - `evidence12` and a fresh TRNG salt go into `presenceHash`, which is what the contract checks;
  - the evidence, salt, signature and CBOR buffers are wiped once the QR text is built, and the QR text is wiped when the screen is left.
- **Keys:**
  - K1 (secp256k1, `m/44'/60'/0'/0/0`) signs only mandates and BindDevice. P1 (P-256, `m/7951'/0'`) signs everything else.
  - Each private key is derived for one signature, the signature is verified (K1 is also recovered) before release, and the key is then wiped.
  - Signatures are RFC 6979 and low-s.
- **Radio.**
  - **`ripar-airgap`: no radio code.** `src/ble_link.cpp`, `src/ble_proto.cpp`, `src/wifi_link.cpp` and `src/wifi_proto.cpp` are not built, nothing else includes the Bluetooth or Wi-Fi headers, and the framework's `BLE`, `WiFi`, `WebServer` and `ESPmDNS` libraries are ignored. Radio check on the linked `firmware.elf` (2026-09-27): `xtensa-esp32s3-elf-nm -C .pio/build/ripar-airgap/firmware.elf | grep -E "esp_wifi_init|esp_bt_controller_init|esp_phy_enable|lwip"` gives **0 matches** (again on 2026-09-28, also for `chk_device`). What remains is code the SDK links unconditionally, not radio code: `esp_bt_controller_mem_release` (called by Arduino's start-up only when `btInUse()` is false, which the framework's ESP32-S3 default is not), the coexistence pre-init stubs from IDF start-up, a Wi-Fi log-level constructor and an empty PHY hook. ROM function addresses from the ROM linker scripts also appear, but they are not linked code.
  - **`ripar-ble`: Bluetooth LE only when the user turns it on, no Wi-Fi code.** The controller is never initialised at boot; only the device menu's BLE LINK (review + pulse + SIGN) starts it, and BLE OFF, PANIC, 5 min without link traffic and power-off stop it (disable + deinit). While it is alive every screen shows **RADIO ON**. The link is LE Secure Connections with numeric comparison confirmed on the device, one bonded phone, and no GATT access without that authenticated link; it only delivers UR parts to SCAN, the same intake as the camera ([BLE_LINK.md](BLE_LINK.md) §3). The same nm check lists `esp_bt_controller_init` / `esp_phy_enable` (Bluetooth) and no `esp_wifi_init`, `esp_wifi_start`, `esp_netif` or `lwip`.
  - **`ripar` (default, for testing): Bluetooth as above, plus the Wi-Fi test link.** Wi-Fi starts only with a network the user confirmed on the device (sent by the bonded phone over BLE) and after WI-FI ON in the menu; that choice is persisted, so such a device is **not air-gapped from boot** until WI-FI OFF / FORGET WI-FI / PANIC. While the driver is alive every screen shows **WIFI ON**. Every HTTP request needs the per-boot 8-digit code shown only on the device; the link only delivers UR parts to SCAN and reads STATUS and the QR on screen ([WIFI_LINK.md](WIFI_LINK.md) §6). Plain HTTP: anyone who can read the network traffic sees the code and the URs.
- **Only one port.** The data USB-C port is the only way in besides the camera. The serial log prints status lines only: self-test results, the K1 address, the pairing chain and "output <type>". It never prints keys or request contents.

## Known limitations

- **Wi-Fi test link not tested on hardware** (`ripar` build, TEMPORARY TEST FEATURE). The PROV write over a real BLE link, association, DHCP, mDNS, HTTP from real clients, coexistence with an active BLE link, WI-FI ON / OFF cycles, the start at boot, heap and power use have never run; only `wifi_proto.cpp` and the state-machine additions are host-tested (`test_wifi_link.cpp`). While Wi-Fi is on the device is on the local network over plain HTTP; the network's password sits in NVS unencrypted. Flash `ripar-airgap` for anything that is not a test.
- **Bluetooth fallback not tested on hardware** (`ripar` and `ripar-ble` builds). Controller start / stop cycles, advertising, pairing with real phones (numeric comparison, the one-bond rule with phones that use resolvable private addresses, the MITM flag Bluedroid reports when a bonded phone re-encrypts), GATT access, notifications, pacing, throughput, the 5-minute auto-off and power use have never run. Only the portable parts (`ble_proto.cpp`, the state-machine additions) are host-tested. While the radio is on, the Bluetooth stack on the same chip as the keys is reachable over the air: keep it off unless needed, or flash `ripar-airgap`. The bond keys are stored by Bluedroid in NVS, unencrypted.
- **Hardware not tested.** The display rotation, the camera orientation and exposure, QR decoding at real distances, MAX30102 detection on real thumbs, the key timings, the buzzer, the battery gauge and the NVS behaviour have not been checked on a board. Everything above comes from the build and the host tests.
- **Crypto is not constant-time.** The ECDSA arithmetic in `crypto.cpp` leaks timing, and the stack used by the point arithmetic is not wiped. This is accepted for an air-gapped prototype that signs only after a physical confirmation. The ESP32-S3 hardware accelerators are not used for private-key operations.
- **The seed is not encrypted.**
  - It sits in NVS as a plain blob. `keys_wipe` cannot erase old NVS copies until the page is recycled.
  - USB-Serial/JTAG and ROM download mode stay enabled, so anyone with the device and a cable can dump the flash with `esptool read_flash`.
  - Flash and NVS encryption, secure download mode and the DIS_USB_JTAG eFuse are planned. **Never burn eFuses on the demo unit**, because it cannot be undone.
- **No seed backup.** Losing or erasing the device loses K1, the vault owner. There is no BIP-39 export yet.
- **Compiled-in contracts (security review N2, closed in v1.2 except where noted).**
  - The PulseCosignEnforcer (10143, 143), RiparDeviceRegistry (10143, 143), RiparReputationRelay (10143 `0xE433…9E2`, 143 `0x108B…f06d`) and MockUSD (10143) addresses are the CREATE2 addresses of the contracts v1.2 bytecode. When this firmware was built (2026-09-27) they had **no code yet** on Monad testnet: they must be deployed from exactly that bytecode through the deterministic deployer, otherwise nothing the device signs for them has any effect.
  - Still trusted on first use: the **RiparSentinel** (its address depends on the CRE workflow owner). A malicious pairing could pin a sentinel that never closes the lane; it is shown in full on the pairing review. The sentinel only adds a stop to the AUTO path, so it cannot widen what a mandate allows. (The relay on 143 was trusted on first use too until the v1.2 review; its constructor arguments are public constants, so it is compiled in now, `contracts/test/FirmwarePins.t.sol`.)
  - AUSD on chain 143 in `src/tokens.cpp` is a placeholder. An unlisted token is shown in base units with an UNKNOWN TOKEN warning.
- **Vault (v1.2).** The device only accepts the vault the canonical MetaMask SimpleFactory deploys for K1 with salt 0 (HybridDeleGator v1.3.0 behind an ERC1967Proxy). A vault deployed any other way (another factory, salt or implementation) cannot be used with this device. The vault is only as trustworthy as its DelegationManager (contracts/SPEC.md v1.2 limitations): the canonical DelegationManager's owner can pause it (funds frozen, not stolen; revoke and panic still work).
- **Device time.**
  - There is no real-time clock. Co-sign expiry is checked against the device's "not before" time (pairing clock, or signed co-sign expiries at most 1 day per co-sign, and never earlier than the build floor).
  - The companion supplies the pairing clock, and the user confirms it on screen (red when it jumps more than 30 days).
  - Each approved co-sign can still move the device time up to 1 day ahead of real time. The review shows every expiry in UTC.
  - A device that falls more than a week behind real time must be paired again.
- **One mandate is tracked.**
  - Revoke covers only the last mandate this device signed, and the device forgets it after signing the revoke, so that QR cannot be shown again. PANIC covers every mandate the device signed.
  - A co-sign for any other mandate shows **UNKNOWN MANDATE** as a warning, not a refusal. The device only knows the terms of the last mandate, so instead of the AUTO payee line with caps it says the payee **may become** an AUTO payee of that mandate, with caps it does not know. A revoke forgets the mandate's terms at once, even if the revoke QR is never relayed.
  - A deny needs a mandate with an agent id.
  - PANIC FIRST is a flag, not a list: after a revoke the device cannot tell whether other mandates since the last panic are still live, so it asks for a panic even if the revoked mandate was the only one. A panic is cheap (no pulse) but raises the epoch every later mandate must carry.
  - The device cannot see whether its PANIC QR was relayed. PANIC FIRST clears when the panic is **signed**; relay it before pairing to another chain. The pairing review then says so in red (`PANIC ... Confirm only if the on-chain min epoch of this device key is >= N`), but the device cannot enforce it: if a companion withheld the panic, pair back to that chain (allowed, the flag is clear) and panic again.
- **Sentinel contract.** Reopen assumes the sentinel accepts any nonce greater than the last one it saw.
- **Privy keys.** The key-quorum `public_keys` format is assumed to be base64 DER SPKI (uncompressed P-256). This has not been checked against Privy's live API.
- **Liveness.**
  - The pulse check shows that a finger is on the sensor. It does not prove that the finger belongs to the owner.
  - **Periodic sources with noise** (v1.2 review): the cross-channel test rejects a strictly periodic source (sine, square, triangle, a replayed PPG beat) plus sensor noise in the host sweep (0 of 960 runs at noise 8–120, 50–130 bpm, 0.5–4 %), but it is a significance test: per evaluation such a source passes with probability ~0.1 %, and at noise at or above the pulse amplitude one run in a few hundred still passes (1 of 480 at noise 250 / 500). A source with random timing common to both channels (a PPG replayed with variability, or amplitude noise from the source itself) is not stopped, nor one that drives IR and red with independent timing.
  - **Weak real pulses pass later** (v1.2 review): the gate only credits variability that both channels share, so it needs the heart's beat-to-beat variability to stand out from the red channel's timing noise. Clean pulses still pass in 5–8 s (up to ~10 s at 42–45 bpm); weak or noisy ones (0.4 % perfusion at noise 20, or 1 % at noise 40 with wander) at rest in up to ~15 s, at 100 bpm in up to ~30 s; at 150–175 bpm with ~1 % RR variability they may not pass at all. Press the thumb flat and still for a stronger signal.
  - The LED-drive challenge is compiled out by default (`RIPAR_LED_CHALLENGE`).
  - Co-sign and deny responses return the raw 12-byte evidence (bpm, DC levels, jitter) to the companion. The contract only sees `presenceHash`.
- **Review paging only moves forward.** To read a review again from the top, cancel (hold 2 s) and scan again.
- **Deny from a co-sign review** needs a relay pinned at pairing and a mandate with an agent id. Otherwise the device explains why and signs nothing.
- **Lost context (older layout v1 / v2, e.g. after updating from firmware v1.1; corrupt NVS).** The device counts as unpaired and its panic epoch and reopen nonce restart at 0. It says so at boot (**PAIRING LOST**). A PANIC or REOPEN signed now would be refused on chain (the enforcer needs a `minEpoch` above its current one, the sentinel a nonce above the last one), so **pair again with the floors**: `make_request.py build pair ... minEpoch=<the enforcer's current minEpoch for this device key, from its latest Panic event> reopenNonce=<the sentinel's last nonce for the vault>`. The floors come from the untrusted companion but can only raise the counters (restrict-only), and both are shown on the pairing review. Mandates signed before the context was lost (for example with firmware v1.1) are no longer tracked: the device forgets their hash and starts with PANIC FIRST cleared, so it would not stop a later pairing to another chain for them. If any of them may still be live, sign a PANIC right after pairing with the floors (and relay it): it kills every mandate whose epoch is at most the floor, so the minEpoch floor must be at least the highest epoch those mandates carry (a v1.1 panic that was signed but never relayed leaves the on-chain value below it). A v1.1 pairing may also have pinned a vault other than the one the device now derives; check that mandates and funds are on the derived vault.
- **Key handling on hardware.** The rule that a press only acts on the screen where it began is host-tested in the state machine; the matching `io_flush` swallow in `io.cpp` (timer task + critical section) is not tested on a board.

## 9. Source map

| File | Role |
|---|---|
| `src/main.cpp` | Arduino entry. 32 KB loop-task stack; calls `app_setup` / `app_loop` |
| `src/flows.cpp` | device driver of the state machine: boot, self-test, key creation, scan, parse, review, pulse, sign, QR, NVS |
| `include/fsm.h`, `src/fsm.cpp` | portable screen state machine and signing gate (host-tested: `test/host/test_fsm.cpp`) |
| `include/respond.h`, `src/respond.cpp` | the SIGN step: policy re-check, digest from the parsed request, signature, response, new context (`test_respond.cpp`, byte-equal to the Python reference) |
| `src/protocol.cpp`, `src/json_strict.cpp` | request parsers, digests, response builders (`test_protocol.cpp`) |
| `src/policy.cpp`, `src/review.cpp`, `src/context.cpp`, `src/enforcers.cpp`, `src/tokens.cpp` | pinned-context policy (incl. PANIC FIRST), review lines, caveat decoders, NVS blob layout v3, compiled-in contract and token tables (`test_policy.cpp`) |
| `include/vault.h`, `src/vault.cpp` | the vault derived from K1: SimpleFactory CREATE2 of the ERC1967Proxy + HybridDeleGator initialize (`test_vault.cpp`, known answer checked on Monad testnet) |
| `src/crypto.cpp`, `src/hashes.cpp`, `src/eip712.cpp`, `src/abi.cpp`, `src/cbor.cpp`, `src/ur.cpp` | portable crypto and encodings (`test_crypto`, `test_hashes`, `test_eip712_abi`, `test_cbor_ur`) |
| `src/pulse_algo.cpp` | beat detection (`test_pulse.cpp`) |
| `src/keys.cpp`, `src/store.cpp` | seed, K1 / P1, self-test (mbedTLS cross-check), context in NVS |
| `src/io.cpp`, `src/pulse.cpp`, `src/qrscan.cpp`, `src/ui.cpp` | BOOT key and buzzer, MAX30102, camera + quirc, LovyanGFX screens (incl. the RADIO ON / WIFI ON badge, the Home Wi-Fi line and the BLE pairing screen) |
| `include/ble_link.h`, `src/ble_link.cpp` | `ripar` / `ripar-ble`: the Bluetooth LE fallback courier on Bluedroid (radio on / off, pairing, GATT service incl. PROV in `ripar`, TX pacing, auto-off) |
| `include/ble_proto.h`, `src/ble_proto.cpp` | `ripar` / `ripar-ble`: its portable logic - RX line reassembly, TX chunking, STATUS JSON (incl. the Wi-Fi keys), idle timer, pairing-outcome rule, UUIDs (`test_ble_link.cpp`) |
| `include/wifi_link.h`, `src/wifi_link.cpp` | `ripar` only, TEMPORARY TEST FEATURE: the Wi-Fi test link (stored network in NVS `ripar-wifi`, station mode, mDNS, the non-blocking HTTP server on port 80) |
| `include/wifi_proto.h`, `src/wifi_proto.cpp` | `ripar` only: its portable logic - PROV JSON, link code + lock-out, HTTP reader and routes (`test_wifi_link.cpp`) |
| `tools/make_request.py`, `tools/ref_*.py` | companion-side builder and verifier; independent Python references |
| `tools/companion_lite.html` | static page: request QR animation, response → verify command |
| `test/device/check_main.cpp` | `chk_device` bring-up program (screens, sensors, self-test; no signing flows) |
