nickthelegend/ripar-wallet/model/parts/Board_PCB.SLDPRT

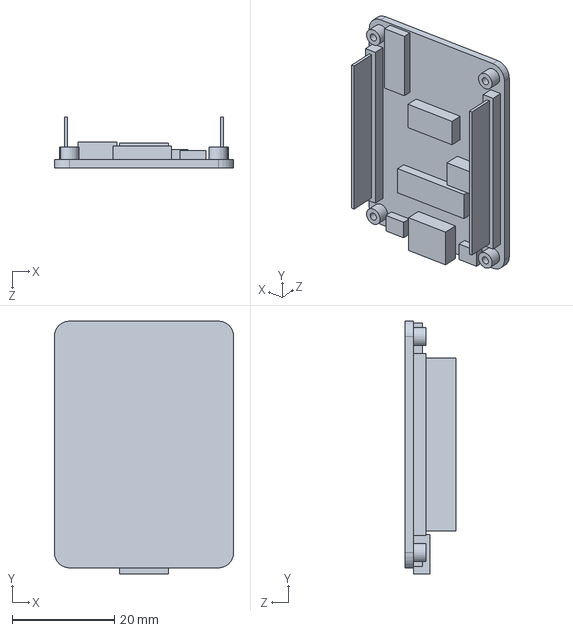
[picture p16: CAD file, 2026-09-26]
model/parts/Board_PCB.SLDPRT
35.0 x 49.4 x 9.90 mm
