nickthelegend/ripar-wallet/model/parts/Latch_Switch_12mm.SLDPRT

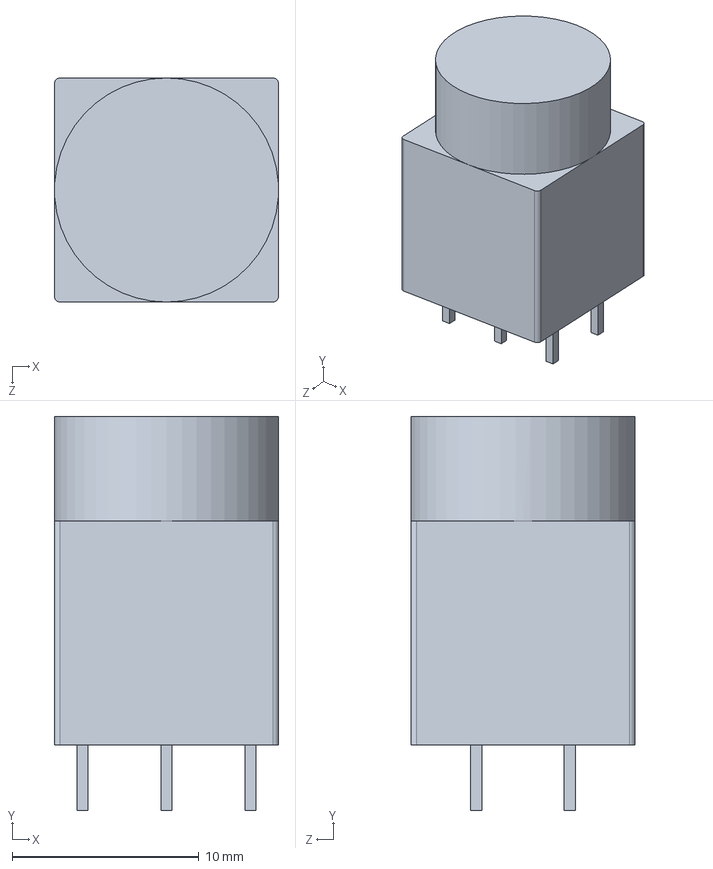
[picture p17: CAD file, 2026-09-26]
model/parts/Latch_Switch_12mm.SLDPRT
12.0 x 21.1 x 12.0 mm
