nickthelegend/ripar-wallet/model/parts/MAX30102.SLDPRT

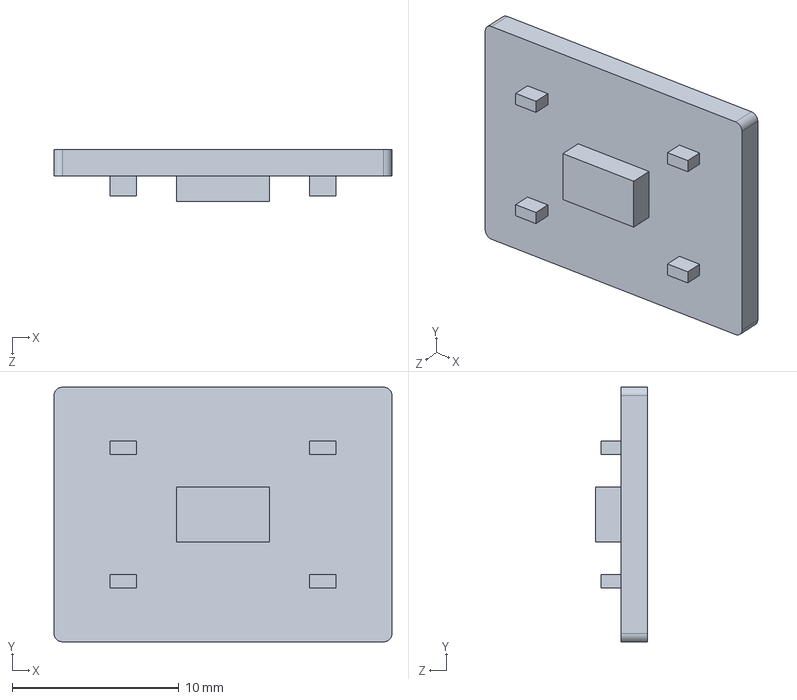
[picture p18: CAD file, 2026-09-26]
model/parts/MAX30102.SLDPRT
20.3 x 15.3 x 3.15 mm
