nickthelegend/ripar-wallet/firmware/src/vault.cpp

// Canonical vault derivation (include/vault.h). Portable C++14 (host + device); needs hashes (keccak256) and
// util only. The constants are the same on Monad testnet (10143) and Monad (143): MetaMask delegation-framework
// v1.3.0 documents/Deployments.md, checked on 10143 (contracts/.work/vault-derivation.md).
#include "vault.h"

#include <cstring>

#include "hashes.h"

namespace ripar {

const char VAULT_SIMPLE_FACTORY[] = "0x69Aa2f9fe1572F1B640E1bbc512f5c3a734fc77c";
const char VAULT_IMPLEMENTATION[] = "0x48dBe696A4D990079e039489bA2053B36E8FFEC4";
const char VAULT_INITIALIZE_SIGNATURE[] = "initialize(address,string[],uint256[],uint256[])";

// ERC1967Proxy creation code, 1008 bytes, exactly @metamask/delegation-abis@2.0.0 dist/bytecode/ERC1967Proxy
// (contracts/.work/ERC1967Proxy.creation.hex). keccak256 = 0xc8fb9314d27cddb08b374dd2bf47cd06c6fb879756ddfbedf522a8c58756a8e0
// (test/host/test_vault.cpp checks it).
const uint8_t VAULT_PROXY_CREATION_CODE[VAULT_PROXY_CREATION_SIZE] = {
    0x60, 0x80, 0x60, 0x40, 0x52, 0x60, 0x40, 0x51, 0x61, 0x03, 0xf0, 0x38, 0x03, 0x80, 0x61, 0x03,
    0xf0, 0x83, 0x39, 0x81, 0x01, 0x60, 0x40, 0x81, 0x90, 0x52, 0x61, 0x00, 0x22, 0x91, 0x61, 0x02,
    0x5e, 0x56, 0x5b, 0x61, 0x00, 0x2c, 0x82, 0x82, 0x61, 0x00, 0x33, 0x56, 0x5b, 0x50, 0x50, 0x61,
    0x03, 0x41, 0x56, 0x5b, 0x61, 0x00, 0x3c, 0x82, 0x61, 0x00, 0x91, 0x56, 0x5b, 0x60, 0x40, 0x51,
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
}

void put_word_addr(uint8_t* w, const Addr& a) {
  std::memset(w, 0, 12);
  std::memcpy(w + 12, a.v, 20);
}

Addr table_addr(const char* hex) {
  Addr a;
  addr_from_hex(hex, a);  // compile-time constants (host-tested); never "" here
  return a;
}

}  // namespace

Bytes vault_initialize_calldata(const Addr& owner) {
  // head: owner, offset(string[]) = 0x80, offset(uint256[]) = 0xa0, offset(uint256[]) = 0xc0; tails: three empty
  // arrays (a length word 0 each)
  Bytes out(4 + 7 * 32, 0);
  uint8_t sel[32];
  keccak256(reinterpret_cast<const uint8_t*>(VAULT_INITIALIZE_SIGNATURE), std::strlen(VAULT_INITIALIZE_SIGNATURE), sel);
  std::memcpy(out.data(), sel, 4);
  uint8_t* w = out.data() + 4;
  put_word_addr(w, owner);
  put_word_u64(w + 32, 0x80);
  put_word_u64(w + 64, 0xa0);
  put_word_u64(w + 96, 0xc0);
  // w + 128 .. w + 224: three zero length words (already zero)
  return out;
}

Bytes vault_constructor_args(const Addr& owner) {
  // abi.encode(address, bytes): head = impl, offset 0x40; tail = length, data right-padded to a multiple of 32
  const Bytes init = vault_initialize_calldata(owner);
  const size_t padded = (init.size() + 31) / 32 * 32;
  Bytes out(64 + 32 + padded, 0);
  put_word_addr(out.data(), table_addr(VAULT_IMPLEMENTATION));
  put_word_u64(out.data() + 32, 0x40);
  put_word_u64(out.data() + 64, init.size());
  std::memcpy(out.data() + 96, init.data(), init.size());
  return out;
}

B32 vault_init_code_hash(const Addr& owner) {
  const Bytes args = vault_constructor_args(owner);
  Keccak256 k;
  k.update(VAULT_PROXY_CREATION_CODE, VAULT_PROXY_CREATION_SIZE);
  k.update(args.data(), args.size());
  B32 h;
  k.final(h.v);
  return h;
}

Addr vault_address(const Addr& owner) {
  uint8_t pre[1 + 20 + 32 + 32];
  pre[0] = 0xff;
  std::memcpy(pre + 1, table_addr(VAULT_SIMPLE_FACTORY).v, 20);
  std::memset(pre + 21, 0, 32);  // salt = bytes32(0)
  std::memcpy(pre + 53, vault_init_code_hash(owner).v, 32);
  uint8_t h[32];
  keccak256(pre, sizeof pre, h);
  Addr a;
  std::memcpy(a.v, h + 12, 20);
  return a;
}

}  // namespace ripar
