nickthelegend/ripar-wallet/firmware/src/crypto.cpp

// Portable crypto for Ripar Wallet (include/crypto.h). Host (g++ -std=c++14) + device (gnu++17, Xtensa).
//
//   SHA-512, HMAC-SHA256/512
//   256-bit Montgomery arithmetic (8 x 32-bit limbs, CIOS) used for both field (mod p) and scalar (mod n) math
//   secp256k1 (a = 0) and P-256 (a = -3) in Jacobian coordinates, 4-bit fixed windows; the i*G table
//   (i = 0..15, affine-normalised) is built once per curve on first use and cached in .bss
//   ECDSA: RFC 6979 nonces (HMAC-SHA256, h1 = the 32-byte digest), low-s, recid, verify, recover, strict DER
//   BIP-32 (secp256k1) and SLIP-10 (nist256p1) private derivation
//
// Conventions / deviations (all mirrored by tools/ref_crypto.py):
//   * If a nonce k gives R.x >= n (prob. ~2^-128 on secp256k1, ~2^-64 on P-256) it is rejected like r == 0 and
//     the RFC 6979 loop continues (K = HMAC_K(V||0x00), V = HMAC_K(V)). So recid is always 0/1, never 2/3.
//   * ecdsa_verify accepts high-s too (plain ECDSA). ecdsa_sign only ever emits low-s.
//   * BIP-32 on secp256k1: an invalid master/child key returns false (no retry). SLIP-10 retry on P-256.
//   * NOT constant-time (branches/table lookups depend on secrets). Accepted for the air-gapped prototype.
//   * Secrets held in this file's own locals are wiped; stack left behind by the inner point arithmetic is not.
//   * The per-curve parameter/table cache is initialised lazily without locking: first use must not race
//     (the device calls crypto from one task only).
#include "crypto.h"

#include <cstring>

#include "hashes.h"

namespace ripar {

namespace {

void wipe(void* p, size_t n) {
  volatile uint8_t* v = static_cast<volatile uint8_t*>(p);
  while (n--) *v++ = 0;
}

// ======================================================================== SHA-512 (FIPS 180-4)
const uint64_t K512[80] = {
    0x428a2f98d728ae22ull, 0x7137449123ef65cdull, 0xb5c0fbcfec4d3b2full, 0xe9b5dba58189dbbcull,
    0x3956c25bf348b538ull, 0x59f111f1b605d019ull, 0x923f82a4af194f9bull, 0xab1c5ed5da6d8118ull,
    0xd807aa98a3030242ull, 0x12835b0145706fbeull, 0x243185be4ee4b28cull, 0x550c7dc3d5ffb4e2ull,
    0x72be5d74f27b896full, 0x80deb1fe3b1696b1ull, 0x9bdc06a725c71235ull, 0xc19bf174cf692694ull,
    0xe49b69c19ef14ad2ull, 0xefbe4786384f25e3ull, 0x0fc19dc68b8cd5b5ull, 0x240ca1cc77ac9c65ull,
    0x2de92c6f592b0275ull, 0x4a7484aa6ea6e483ull, 0x5cb0a9dcbd41fbd4ull, 0x76f988da831153b5ull,
    0x983e5152ee66dfabull, 0xa831c66d2db43210ull, 0xb00327c898fb213full, 0xbf597fc7beef0ee4ull,
    0xc6e00bf33da88fc2ull, 0xd5a79147930aa725ull, 0x06ca6351e003826full, 0x142929670a0e6e70ull,
    0x27b70a8546d22ffcull, 0x2e1b21385c26c926ull, 0x4d2c6dfc5ac42aedull, 0x53380d139d95b3dfull,
    0x650a73548baf63deull, 0x766a0abb3c77b2a8ull, 0x81c2c92e47edaee6ull, 0x92722c851482353bull,
    0xa2bfe8a14cf10364ull, 0xa81a664bbc423001ull, 0xc24b8b70d0f89791ull, 0xc76c51a30654be30ull,
    0xd192e819d6ef5218ull, 0xd69906245565a910ull, 0xf40e35855771202aull, 0x106aa07032bbd1b8ull,
    0x19a4c116b8d2d0c8ull, 0x1e376c085141ab53ull, 0x2748774cdf8eeb99ull, 0x34b0bcb5e19b48a8ull,
    0x391c0cb3c5c95a63ull, 0x4ed8aa4ae3418acbull, 0x5b9cca4f7763e373ull, 0x682e6ff3d6b2b8a3ull,
    0x748f82ee5defb2fcull, 0x78a5636f43172f60ull, 0x84c87814a1f0ab72ull, 0x8cc702081a6439ecull,
    0x90befffa23631e28ull, 0xa4506cebde82bde9ull, 0xbef9a3f7b2c67915ull, 0xc67178f2e372532bull,
    0xca273eceea26619cull, 0xd186b8c721c0c207ull, 0xeada7dd6cde0eb1eull, 0xf57d4f7fee6ed178ull,
    0x06f067aa72176fbaull, 0x0a637dc5a2c898a6ull, 0x113f9804bef90daeull, 0x1b710b35131c471bull,
    0x28db77f523047d84ull, 0x32caab7b40c72493ull, 0x3c9ebe0a15c9bebcull, 0x431d67c49c100d4cull,
    0x4cc5d4becb3e42b6ull, 0x597f299cfc657e2aull, 0x5fcb6fab3ad6faecull, 0x6c44198c4a475817ull,
};

inline uint64_t rotr64(uint64_t x, unsigned n) { return (x >> n) | (x << (64 - n)); }

inline uint64_t load_be64(const uint8_t* p) {
  uint64_t v = 0;
  for (int i = 0; i < 8; i++) v = (v << 8) | p[i];
  return v;
}

inline void store_be64(uint8_t* p, uint64_t v) {
  for (int i = 7; i >= 0; i--) {
    p[i] = uint8_t(v);
    v >>= 8;
  }
}

struct Sha512 {
  uint64_t st[8];
  uint64_t total;  // bytes hashed so far (messages < 2^61 bytes)
  uint8_t buf[128];
  size_t n;

  Sha512() { init(); }
  ~Sha512() { wipe(this, sizeof(*this)); }

  void init() {
    static const uint64_t IV[8] = {0x6a09e667f3bcc908ull, 0xbb67ae8584caa73bull, 0x3c6ef372fe94f82bull,
                                   0xa54ff53a5f1d36f1ull, 0x510e527fade682d1ull, 0x9b05688c2b3e6c1full,
                                   0x1f83d9abfb41bd6bull, 0x5be0cd19137e2179ull};
    std::memcpy(st, IV, sizeof(st));
    total = 0;
    n = 0;
  }

  void block(const uint8_t* p) {
    uint64_t w[16];
    for (int i = 0; i < 16; i++) w[i] = load_be64(p + 8 * i);
    uint64_t a = st[0], b = st[1], c = st[2], d = st[3], e = st[4], f = st[5], g = st[6], hh = st[7];
    for (int i = 0; i < 80; i++) {
      uint64_t wi;
      if (i < 16) {
        wi = w[i];
      } else {
        const uint64_t w15 = w[(i - 15) & 15], w2 = w[(i - 2) & 15];
        const uint64_t s0 = rotr64(w15, 1) ^ rotr64(w15, 8) ^ (w15 >> 7);
        const uint64_t s1 = rotr64(w2, 19) ^ rotr64(w2, 61) ^ (w2 >> 6);
        wi = w[i & 15] = w[i & 15] + s0 + w[(i - 7) & 15] + s1;
      }
      const uint64_t S1 = rotr64(e, 14) ^ rotr64(e, 18) ^ rotr64(e, 41);
      const uint64_t ch = (e & f) ^ (~e & g);
      const uint64_t t1 = hh + S1 + ch + K512[i] + wi;
      const uint64_t S0 = rotr64(a, 28) ^ rotr64(a, 34) ^ rotr64(a, 39);
      const uint64_t maj = (a & b) ^ (a & c) ^ (b & c);
      const uint64_t t2 = S0 + maj;
      hh = g;
      g = f;
      f = e;
      e = d + t1;
      d = c;
      c = b;
      b = a;
      a = t1 + t2;
    }
    st[0] += a;
    st[1] += b;
    st[2] += c;
    st[3] += d;
    st[4] += e;
    st[5] += f;
    st[6] += g;
    st[7] += hh;
    wipe(w, sizeof(w));
  }

  void update(const uint8_t* data, size_t len) {
    if (!len) return;
    total += len;
    if (n) {
      size_t take = 128 - n;
      if (take > len) take = len;
      std::memcpy(buf + n, data, take);
      n += take;
      data += take;
      len -= take;
      if (n < 128) return;
      block(buf);
      n = 0;
    }
    while (len >= 128) {
      block(data);
      data += 128;
      len -= 128;
    }
    if (len) {
      std::memcpy(buf, data, len);
      n = len;
    }
  }

  void final(uint8_t out[64]) {
    const uint64_t bits = total << 3;
    uint8_t pad[128 + 16];
    std::memset(pad, 0, sizeof(pad));
    pad[0] = 0x80;
    // pad to 112 mod 128, then the 128-bit big-endian bit length (high 64 bits are 0)
    size_t padlen = (n < 112) ? (112 - n) : (240 - n);
    store_be64(pad + padlen + 8, bits);
    update(pad, padlen + 16);
    for (int i = 0; i < 8; i++) store_be64(out + 8 * i, st[i]);
    init();
  }
};

// ======================================================================== 256-bit integers
struct Big {
  uint32_t w[8];  // little-endian 32-bit limbs
};

const Big BIG_ONE = {{1, 0, 0, 0, 0, 0, 0, 0}};

inline void big_zero(Big& r) { std::memset(r.w, 0, sizeof(r.w)); }

inline bool big_is_zero(const Big& a) {
  uint32_t x = 0;
  for (int i = 0; i < 8; i++) x |= a.w[i];
  return x == 0;
}

inline bool big_eq(const Big& a, const Big& b) { return std::memcmp(a.w, b.w, sizeof(a.w)) == 0; }

int big_cmp(const Big& a, const Big& b) {
  for (int i = 7; i >= 0; i--) {
    if (a.w[i] != b.w[i]) return a.w[i] < b.w[i] ? -1 : 1;
  }
  return 0;
}

uint32_t big_add(Big& r, const Big& a, const Big& b) {
  uint64_t c = 0;
  for (int i = 0; i < 8; i++) {
    c += uint64_t(a.w[i]) + b.w[i];
    r.w[i] = uint32_t(c);
    c >>= 32;
  }
  return uint32_t(c);
}

uint32_t big_sub(Big& r, const Big& a, const Big& b) {
  uint32_t borrow = 0;
  for (int i = 0; i < 8; i++) {
    const uint64_t d = uint64_t(a.w[i]) - b.w[i] - borrow;
    r.w[i] = uint32_t(d);
    borrow = uint32_t(d >> 63);  // 1 if it wrapped
  }
  return borrow;
}

void big_shr1(Big& r, const Big& a) {
  for (int i = 0; i < 8; i++) r.w[i] = (a.w[i] >> 1) | (i < 7 ? (a.w[i + 1] << 31) : 0u);
}

void big_from_be(Big& r, const uint8_t* b) {
  for (int i = 0; i < 8; i++) {
    const uint8_t* p = b + 28 - 4 * i;
    r.w[i] = (uint32_t(p[0]) << 24) | (uint32_t(p[1]) << 16) | (uint32_t(p[2]) << 8) | p[3];
  }
}

void big_to_be(uint8_t* b, const Big& a) {
  for (int i = 0; i < 8; i++) {
    uint8_t* p = b + 28 - 4 * i;
    p[0] = uint8_t(a.w[i] >> 24);
    p[1] = uint8_t(a.w[i] >> 16);
    p[2] = uint8_t(a.w[i] >> 8);
    p[3] = uint8_t(a.w[i]);
  }
}

// constants only: exactly 64 hex digits
void big_from_hex(Big& r, const char* s) {
  uint8_t b[32];
  for (int i = 0; i < 32; i++) {
    uint8_t v = 0;
    for (int j = 0; j < 2; j++) {
      const char c = s[2 * i + j];
      const uint8_t d = uint8_t(c <= '9' ? c - '0' : (c | 0x20) - 'a' + 10);
      v = uint8_t((v << 4) | d);
    }
    b[i] = v;
  }
  big_from_be(r, b);
}

inline unsigned big_nibble(const Big& k, int i) { return (k.w[i >> 3] >> ((i & 7) * 4)) & 15u; }

// ======================================================================== Montgomery arithmetic mod an odd m > 2^255
struct Mod {
  Big m;
  Big one;      // R mod m (Montgomery form of 1), R = 2^256
  Big r2;       // R^2 mod m
  Big m_minus2; // inversion exponent (m prime)
  uint32_t minv;  // -m^-1 mod 2^32
};

// r = a + b mod m (a, b < m)
void mod_add(Big& r, const Big& a, const Big& b, const Mod& M) {
  const uint32_t c = big_add(r, a, b);
  if (c || big_cmp(r, M.m) >= 0) big_sub(r, r, M.m);
}
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
